Perth-Artifactory/artifactory-draw-matrix/photos/IMG_20190930_150919.jpg

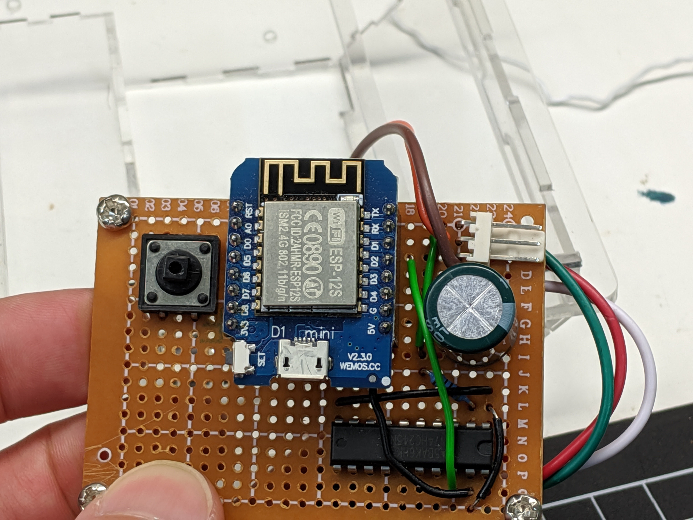
photos/IMG_20190930_150919.jpg
