Perth-Artifactory/artifactory-draw-matrix/photos/IMG_20190930_151024.jpg

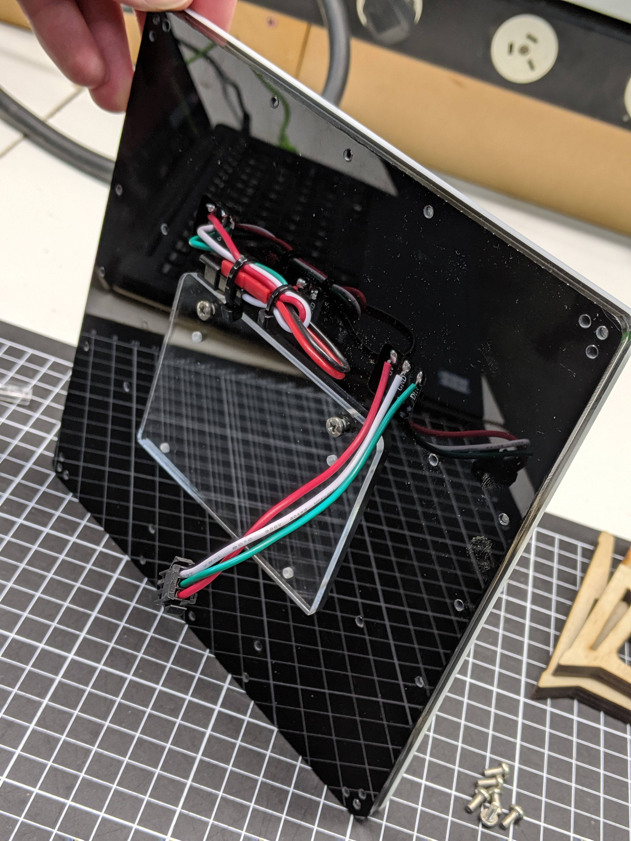
photos/IMG_20190930_151024.jpg
