Perth-Artifactory/artifactory-draw-matrix/photos/IMG_20190930_151056.jpg

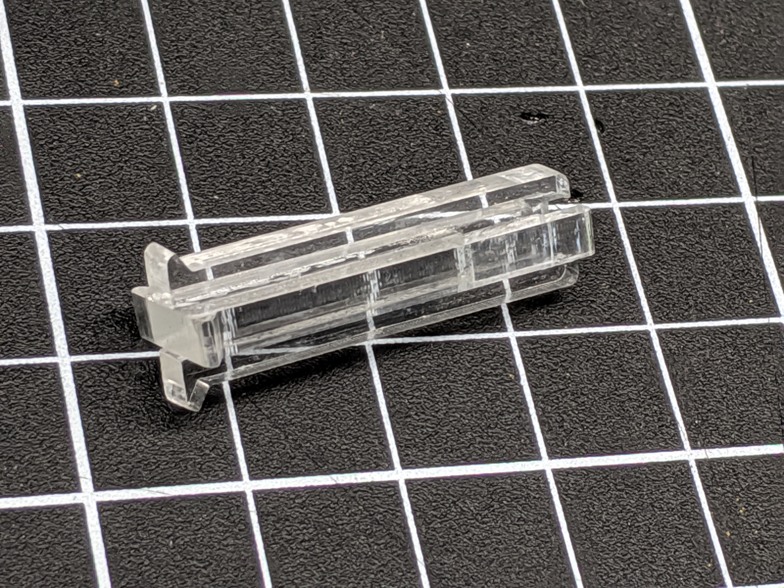
photos/IMG_20190930_151056.jpg
