Perth-Artifactory/artifactory-draw-matrix/cad_files/16x16/complete/back cutout.dxf

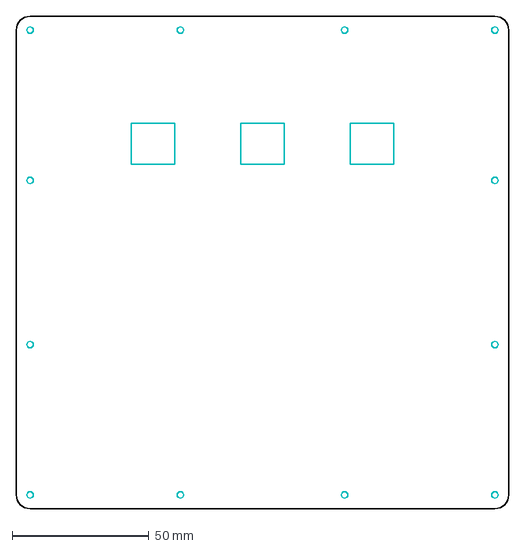
[picture p23: CAD file, 2019-09-30]
cad_files/16x16/complete/back cutout.dxf
180.0 x 180.0 mm
