Perth-Artifactory/artifactory-draw-matrix/cad_files/16x16/side05.dxf

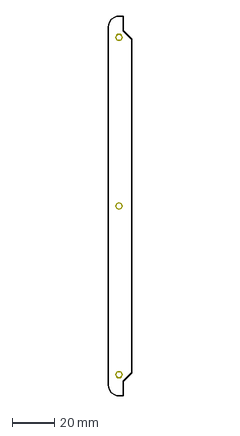
[picture p24: CAD file, 2019-09-30]
cad_files/16x16/side05.dxf
11.0 x 180.0 mm
