Perth-Artifactory/artifactory-draw-matrix/cad_files/32x8/Back.dxf

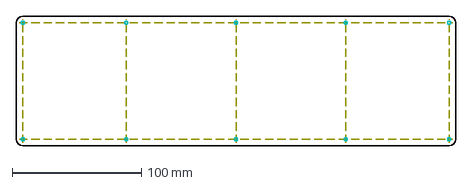
[picture p25: CAD file, 2019-09-30]
cad_files/32x8/Back.dxf
340.0 x 100.0 mm
