Perth-Artifactory/artifactory-draw-matrix/cad_files/32x8/Complete/back.dxf

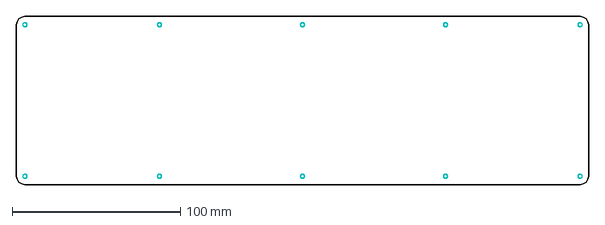
[picture p26: CAD file, 2019-09-30]
cad_files/32x8/Complete/back.dxf
340.0 x 100.0 mm
