Perth-Artifactory/artifactory-draw-matrix/cad_files/16x16/Front.dxf

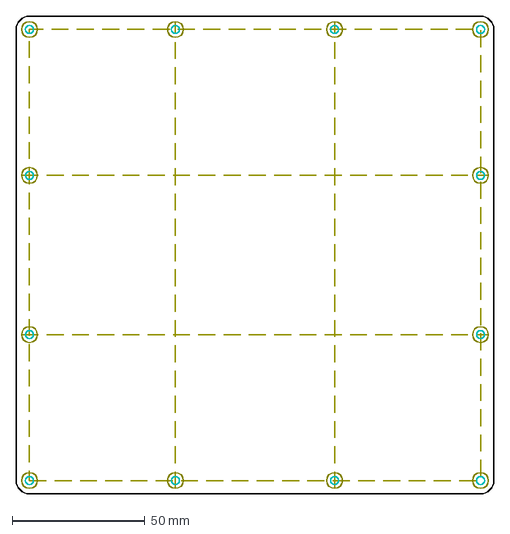
[picture p27: CAD file, 2019-09-30]
cad_files/16x16/Front.dxf
180.0 x 180.0 mm
