Perth-Artifactory/artifactory-draw-matrix/cad_files/16x16/back cutout03.dxf

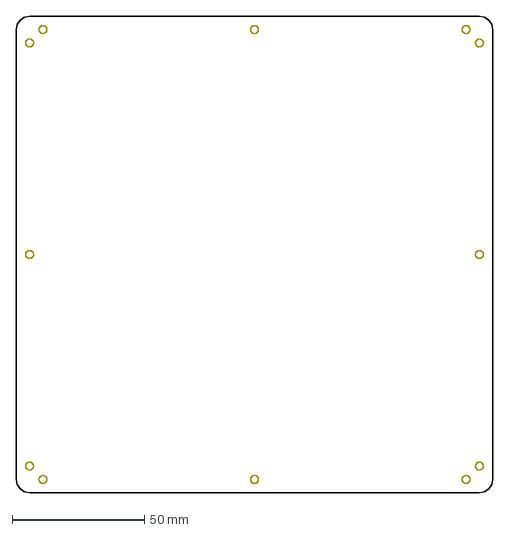
[picture p28: CAD file, 2019-09-30]
cad_files/16x16/back cutout03.dxf
180.0 x 180.0 mm
