Perth-Artifactory/artifactory-draw-matrix/cad_files/16x16/back cutout02.dxf

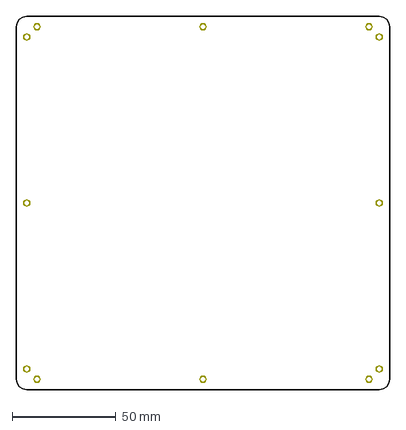
[picture p31: CAD file, 2019-09-30]
cad_files/16x16/back cutout02.dxf
180.0 x 180.0 mm
