Perth-Artifactory/artifactory-draw-matrix/pixart.h

// Can use LED Matrix Studio to create these
// https://sourceforge.net/projects/led-matrix-studio/


uint32_t pixart_artifactory_logo[] = {
    0x00000000, 0x00000000, 0x00000000, 0x00000000, 0x00000000, 0x00000000, 0x00000000, 0x00000000, 0x00000000, 0x00000000, 0x00000000, 0x00000000, 0x00000000, 0x00000000, 0x00000000, 0x00000000, 
    0x00000000, 0x00000000, 0x00000000, 0x00000000, 0x00000000, 0x00101010, 0x00787878, 0x00797979, 0x00797979, 0x00787878, 0x00131313, 0x00000000, 0x00000000, 0x00000000, 0x00000000, 0x00000000, 
    0x00000000, 0x00000000, 0x00000000, 0x00000000, 0x00000000, 0x007D7D7D, 0x00575757, 0x00313131, 0x00313131, 0x00535353, 0x00828282, 0x00000000, 0x00000000, 0x00000000, 0x00000000, 0x00000000, 
    0x00000000, 0x00000000, 0x00000000, 0x00000000, 0x00090909, 0x00AEAEAE, 0x00000000, 0x00000000, 0x00000000, 0x00000000, 0x00ADADAD, 0x000A0A0A, 0x00000000, 0x00000000, 0x00000000, 0x00000000, 
    0x00000000, 0x00000000, 0x00000000, 0x00000000, 0x00696969, 0x004F4F4F, 0x00000000, 0x00000000, 0x000D0D0D, 0x00000000, 0x004D4D4D, 0x006B6B6B, 0x00000000, 0x00000000, 0x00000000, 0x00000000, 
    0x00000000, 0x00000000, 0x00000000, 0x00030303, 0x00B3B3B3, 0x00020202, 0x00000000, 0x00323232, 0x00808080, 0x00000000, 0x00020202, 0x00B3B3B3, 0x00030303, 0x00000000, 0x00000000, 0x00000000, 
    0x00000000, 0x00000000, 0x00000000, 0x00525252, 0x00B8B8B8, 0x00737373, 0x00737373, 0x00B9B9B9, 0x00191919, 0x00000000, 0x00000000, 0x00646464, 0x00535353, 0x00000000, 0x00000000, 0x00000000, 
    0x00000000, 0x00000000, 0x00000000, 0x00131313, 0x00363636, 0x00363636, 0x00363636, 0x00282828, 0x00000000, 0x00000000, 0x00000000, 0x00080808, 0x00B0B0B0, 0x00000000, 0x00000000, 0x00000000, 
    0x00000000, 0x00000000, 0x00000000, 0x00000000, 0x00000000, 0x00000000, 0x00000000, 0x00000000, 0x00000000, 0x00000000, 0x00000000, 0x00000000, 0x007B7B7B, 0x003C3C3C, 0x00000000, 0x00000000, 
    0x00000000, 0x00000000, 0x008D8D8D, 0x00A9A9A9, 0x00A9A9A9, 0x00A9A9A9, 0x00A9A9A9, 0x00A9A9A9, 0x00A9A9A9, 0x00B3B3B3, 0x000F0F0F, 0x00000000, 0x00121212, 0x00A5A5A5, 0x00000000, 0x00000000, 
    0x00000000, 0x00272727, 0x00919191, 0x00000000, 0x00000000, 0x00000000, 0x00000000, 0x00000000, 0x00000000, 0x00434343, 0x00757575, 0x00000000, 0x00000000, 0x00909090, 0x00272727, 0x00000000, 
    0x00000000, 0x00949494, 0x00232323, 0x00000000, 0x00000000, 0x00000000, 0x00000000, 0x00000000, 0x00000000, 0x00000000, 0x00B2B2B2, 0x00050505, 0x00000000, 0x00222222, 0x00969696, 0x00000000, 
    0x00141414, 0x00A3A3A3, 0x00000000, 0x00000000, 0x00555555, 0x004C4C4C, 0x00000000, 0x00000000, 0x00000000, 0x00000000, 0x005A5A5A, 0x005D5D5D, 0x00000000, 0x00000000, 0x00A1A1A1, 0x00161616, 
    0x007C7C7C, 0x007F7F7F, 0x004A4A4A, 0x004A4A4A, 0x00B4B4B4, 0x00060606, 0x00000000, 0x00000000, 0x00000000, 0x00000000, 0x00050505, 0x00B4B4B4, 0x004A4A4A, 0x004A4A4A, 0x007B7B7B, 0x00818181, 
    0x003C3C3C, 0x00606060, 0x00606060, 0x00606060, 0x00383838, 0x00000000, 0x00000000, 0x00000000, 0x00000000, 0x00000000, 0x00000000, 0x00363636, 0x00606060, 0x00606060, 0x00606060, 0x003E3E3E, 
    0x00000000, 0x00000000, 0x00000000, 0x00000000, 0x00000000, 0x00000000, 0x00000000, 0x00000000, 0x00000000, 0x00000000, 0x00000000, 0x00000000, 0x00000000, 0x00000000, 0x00000000, 0x00000000, 
    };                       


// Mario: https://1.bp.blogspot.com/-SN7l3p_K6bc/UjVkFUlYFNI/AAAAAAAAANA/WcTUw9zi9NU/s1600/mario_3501733.jpg

// Pokeball: http://pm1.narvii.com/6328/01a360d15dc058ad413600867860c04e396fc88e_hq.jpg

// Link: https://i.pinimg.com/736x/59/65/9a/59659aaa84ed758fa4f7ef35b497fe7e.jpg

// Lightning: https://www.vhv.rs/dpng/d/418-4187254_16-bit-lightning-bolt-png-download-lightning-bolt.png
