Perth-Artifactory/artifactory-draw-matrix/photos/IMG_20190930_151043.jpg

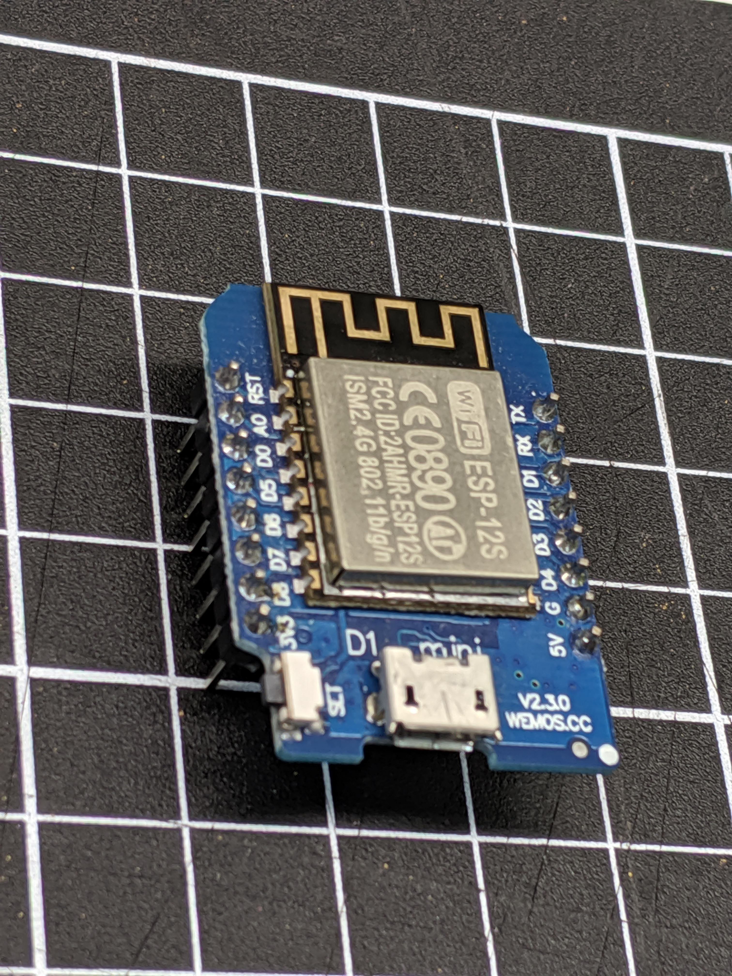
photos/IMG_20190930_151043.jpg
